moonbeeper/echowawa/PCB/symbols/3dshapes/SW-SMD_L3.9-W2.9-H2.0-LS4.8.step

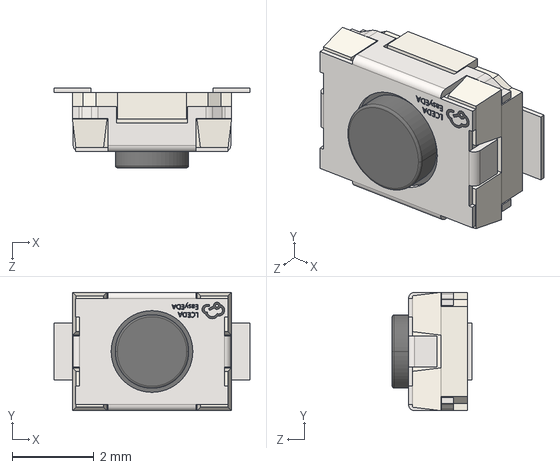
[picture p20: CAD file, 2025-07-28]
PCB/symbols/3dshapes/SW-SMD_L3.9-W2.9-H2.0-LS4.8.step
4.80 x 2.90 x 1.95 mm
